sakg-dev/my-keeb/imgs/pcb.png

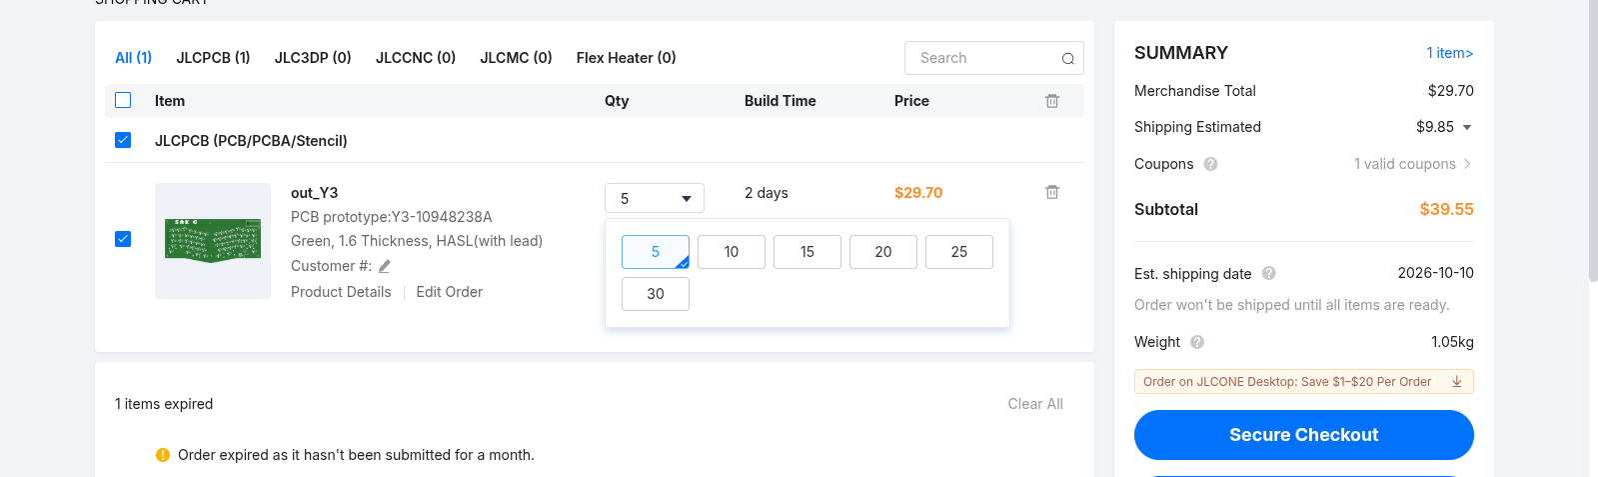
imgs/pcb.png
