sakg-dev/my-keeb/imgs/switches.png

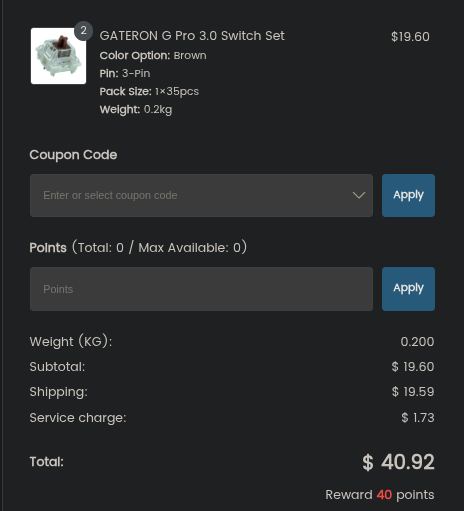
imgs/switches.png
